pyubero/open_tracker/docs/models_3d/stl-files/Finished/tapon_led_update1.stl

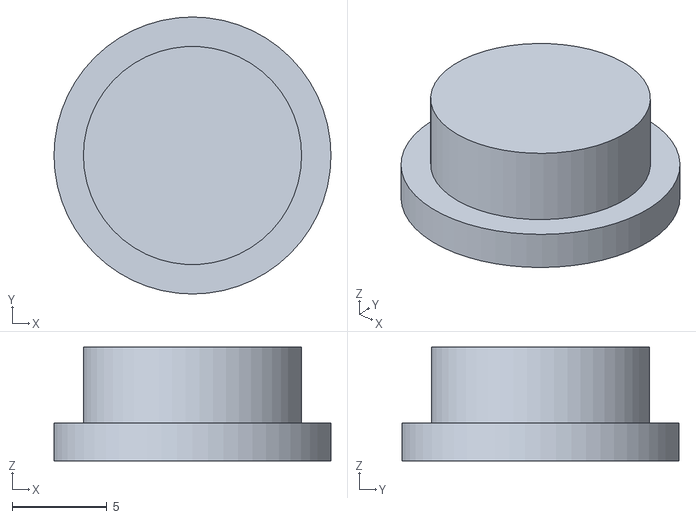
[picture p28: CAD file, 2022-03-09]
docs/models_3d/stl-files/Finished/tapon_led_update1.stl
14.6 x 14.6 x 6.00
