pyubero/open_tracker/docs/models_3d/stl-files/Finished/phase_shifters-shifter_large.stl

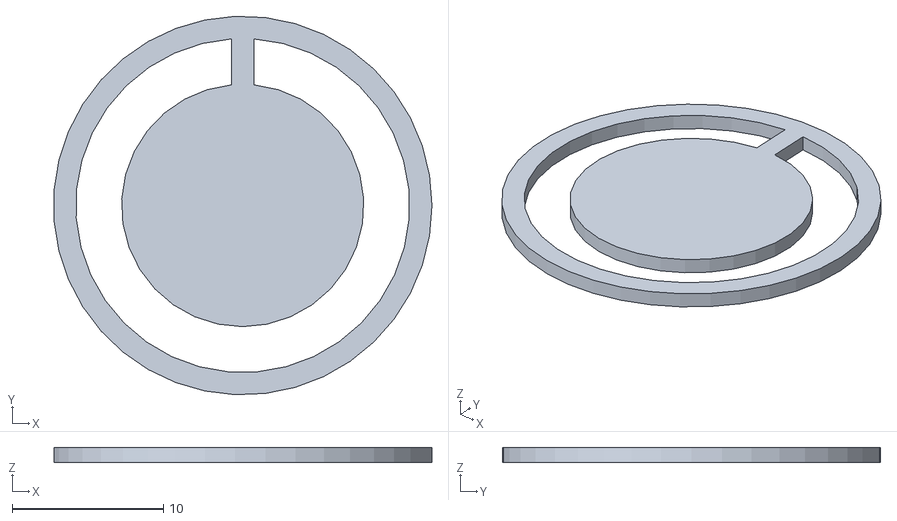
[picture p29: CAD file, 2022-03-09]
docs/models_3d/stl-files/Finished/phase_shifters-shifter_large.stl
25.0 x 25.0 x 1.00
