pyubero/open_tracker/pytracker/myArduino.py

# -*- coding: utf-8 -*-
"""
Created on Wed Aug 25 13:24:23 2021

@author: Pablo
"""

from pymata4 import pymata4
import serial.tools.list_ports
import numpy as np
from time import sleep
import threading
from threading import Thread
from datetime import datetime


class myArduino:
    def __init__(self, device, baudrate=28800):
        print('Initializing arduino...')
        self.board = pymata4.Pymata4(com_port = device, baud_rate = baudrate)
        
        self.total_analog_pins = len(self.board.analog_pins)
        self.total_digital_pins = len(self.board.digital_pins) - self.total_analog_pins
        
        # As with pymata4 the state of output pins cannot be queried, we store 
        # ... their values as they change.
        self.digitalPins = np.zeros( ( self.total_digital_pins,) )
        self._blinking_running = [False    for _ in range(self.total_digital_pins) ]
        self.blink_threads     = [Thread() for _ in range(self.total_digital_pins) ]
        
        self.__setup_blinking_leds()
        self.STATUS_LED_PIN = 13



    def __del__(self):
        self.close()
         
     
        
    def set_mode(self, pin_number, mode, callback = None):
        if mode=='analog_input':
            self.board.set_pin_mode_analog_input(pin_number, callback=callback)
            
        elif mode=='digital_input':
            self.board.set_pin_mode_digital_input(pin_number, callback=callback)
            
        elif mode=='digital_input_pullup':
            self.board.set_pin_mode_digital_input_pullup(pin_number, callback=callback)
        
        elif mode=='digital_output':
            self.board.set_pin_mode_digital_output(pin_number)    

        elif mode=='pwm':
            self.board.set_pin_mode_pwm_output(pin_number)    
        
        elif mode=='servo':
            self.board.set_pin_mode_servo(pin_number)


    def close(self, analog=None , digital=None ):
        # Stop threads
        if self.thread_led_status_running:
            self.thread_led_status_running = False
            self.thread_led_status.join() 
            
        if analog is None:
            analog = range( self.total_analog_pins)
            
        if digital is None:
            digital = range( self.total_digital_pins)
            
            
        # Disable analog and digital reportings
        for pin in analog:
            self.board.disable_analog_reporting(pin)
            sleep(0.02)
        
        for pin in digital:
            self.board.disable_digital_reporting(pin)
            sleep(0.2)
        
        
        # Turn off digital pins
        for pin in digital:
            self.write(pin, 0)
            sleep(0.02)
        
        
        self.board.shutdown()
        print('Arduino communication closed.') 


    #=====================================#
    #    BASIC COMMUNICATING FUNCTIONS    #
    #=====================================#
    def read(self, pin_number, mode='analog',**kwargs):
        '''Here kwargs can be Rvd, Vd, Rref, Tref, Iref'''
        
        if mode =='analog':
            return self.board.analog_read(pin_number)[0]/1023
        
        elif mode =='digital':
            return self.board.digital_read(pin_number)[0]
        
        elif mode =='voltage_divider':
            return a2r( self.read(pin_number, mode='analog'), **kwargs)
        
        elif mode =='temperature':
            return r2t( self.read(pin_number, mode='voltage_divider', **kwargs), **kwargs)
            
        elif mode =='illuminance':
            return r2i( self.read(pin_number, mode='voltage_divider', **kwargs), **kwargs)
        
        
        
    def write(self, pin_number, value, mode='digital'):
        # Store current pin state in our own array
        self.digitalPins[pin_number] = value
        
        # ... and then write value
        if mode =='digital':         
            return self.board.digital_write(pin_number, value)
        
        elif mode=='pwm':
            return self.board.pwm_write( pin_number, value)
        
        elif mode=='servo':
            return self.board.servo_write(pin_number, value)   

        
    def write_pwm(self, pin_number, value):
        return self.board.pwm_write( pin_number, value)


    def write_servo(self, pin_number, angle=0):
        return self.board.servo_write( pin_number, angle)


    
    def toggle(self, pin_number):
        pin_mode = self.board.get_pin_state(pin_number)[1]
        
        if pin_mode == 1: #DIGITAL OUTPUT
            new_value = 1.0 - self.digitalPins[pin_number]
            self.write( pin_number, new_value, mode='digital')
            
        elif pin_mode == 3: #DIGITAL PWM
            new_value = 255 - self.digitalPins[pin_number]
            self.write( pin_number, new_value, mode='pwm')
            
        elif pin_mode == 4: #DIGITAL SERVO
            new_value = 180 - self.digitalPins[pin_number]
            self.write( pin_number, new_value, mode='servo')
        
        else:
            print('<< E >> myArduino.toggle(pin_number) needs a valid digital output pin number')
            return
        
        
    #===============================#
    #    BLINKING LEDS FUNCTIONS    #
    #===============================#
    def __setup_blinking_leds(self):
        self.thread_led_status = Thread()
        self.thread_led_status_running = False
        
        
    def __blink_threadfun_status(self):
        self.thread_led_status_running = True
        DTIME          = 0.3        
        tLast          = datetime.now()
        
        while self.thread_led_status_running:    
            if (datetime.now()-tLast).total_seconds() > DTIME:
                self.toggle(self.STATUS_LED_PIN)
                tLast = datetime.now()
                sleep(0.02)
                
    def start_blink_status(self):
        if self.thread_led_status_running:
            print('<W> Status led is already blinking.')
            return
        else:
            self.thread_led_status = Thread(target= self.__blink_threadfun_status , daemon = True)
            self.thread_led_status.start()






##########################################################
################# SOME UTILITY FUNCTIONS #################
def find_devices(filter_name =None , filter_value =None):
    comports = serial.tools.list_ports.comports()
    
    if filter_value is not None:
        if filter_name == 'pid':
            return [ port.name for port in comports if port.pid == filter_value ]
        if filter_name == 'vid':
            return [ port.name for port in comports if port.pid == filter_value ]
        else:
            print('<W> Please introduce a valid filter_name either "vid" or "pid".')
            return 
    else:
        return [comport.device for comport in serial.tools.list_ports.comports()]
     

def find_arduinos( filter_name = 'pid', filter_value = 29987):
    return find_devices( filter_name=filter_name, filter_value=filter_value)



def a2r( A , rvd = 10_000, vd=+1, **kwargs):
    '''This function returns the resistance measured at a voltage divider in units of Rvd.
    The voltage divider configuration is selected with Vd=+1 or Vd=-1'''
    rvd = float(rvd)
    vd  = float(vd)
    if A==0:
        return 1e-6
    else:
        return rvd*( 1/A -1 )**vd


def r2t( R , rref=10_000, tref=25, beta=4050, **kwargs):
    '''This functions converts the resistance of an NTC into a temperature (ºC)'''
    rref = float(rref)
    tref = float(tref)
    beta = float(beta)
    return (1/(tref+273) + np.log(R/rref)/beta)**-1 -273

    
def r2i( R, rref=10_000, iref= 1000, gamma = 0.65, **kwargs):
    '''This functions converts the resistance of an LDR into luminance (lux)'''
    rref = float(rref)
    iref = float(iref)
    gamma= float(gamma)
    
    return iref*(R/rref)**(-gamma)
    

    
